kylawilson/Senior-Design-Sailboat-Nav-2025/HOUSING/Housing_main.png

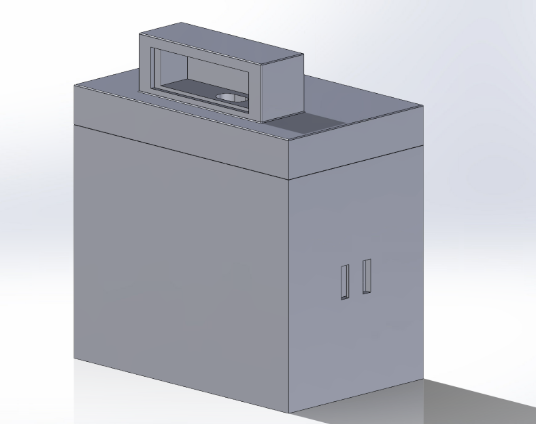
HOUSING/Housing_main.png
