kylawilson/Senior-Design-Sailboat-Nav-2025/HOUSING/Housing_sides.png

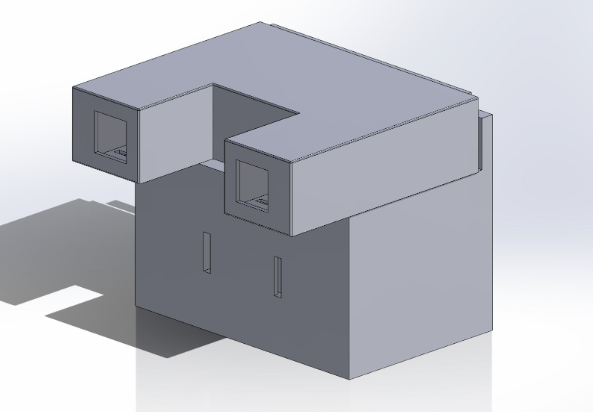
HOUSING/Housing_sides.png
