kylawilson/Senior-Design-Sailboat-Nav-2025/HOUSING/MountPoints.png

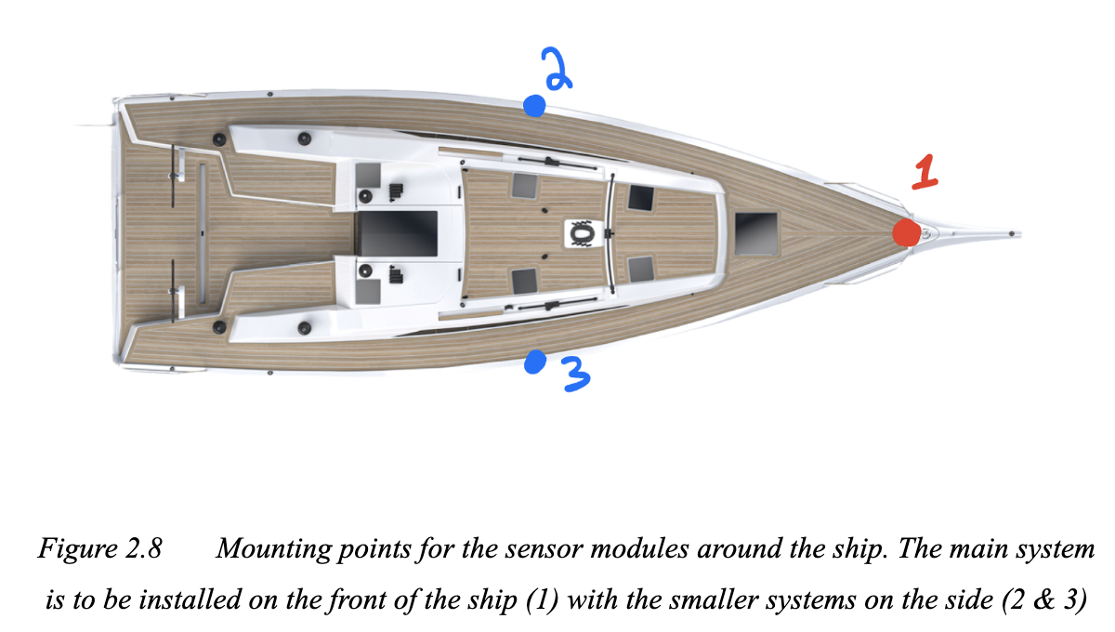
HOUSING/MountPoints.png
