kylawilson/Senior-Design-Sailboat-Nav-2025/OAK-D/outputframe.jpg

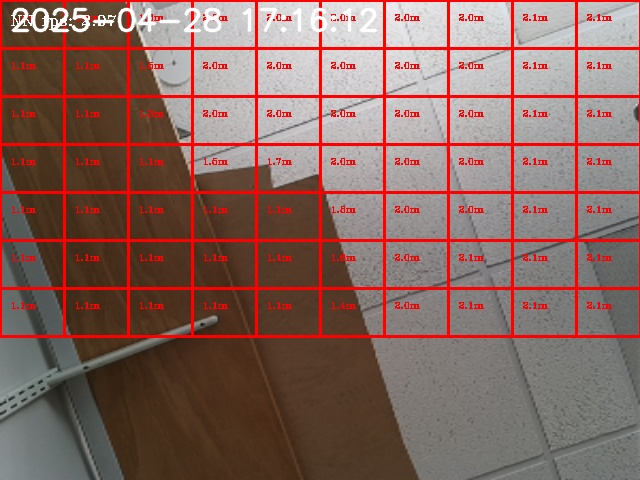
OAK-D/outputframe.jpg
