kylawilson/Senior-Design-Sailboat-Nav-2025/outputframe.jpg

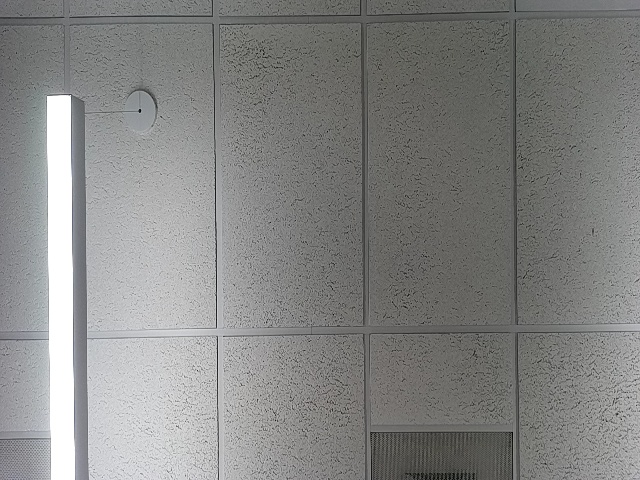
outputframe.jpg
