kylawilson/Senior-Design-Sailboat-Nav-2025/stereopi/normal.jpg

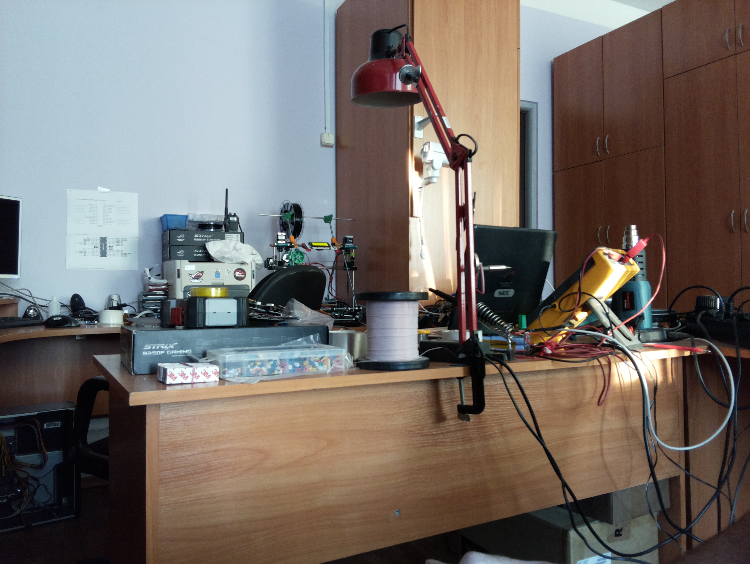
stereopi/normal.jpg
