kylawilson/Senior-Design-Sailboat-Nav-2025/stereopi/pairs/left_05.png

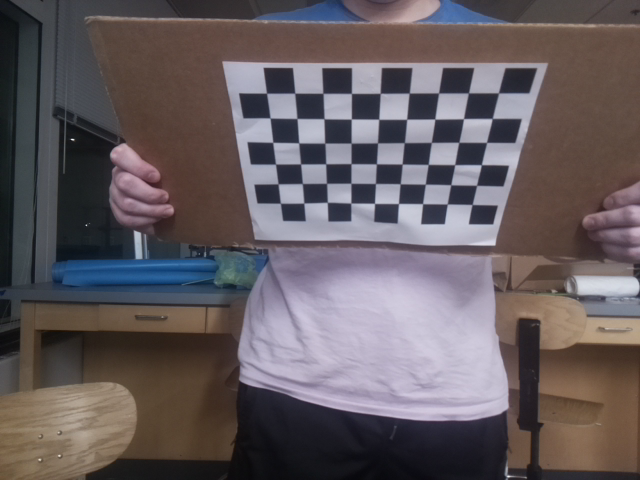
stereopi/pairs/left_05.png
