kylawilson/Senior-Design-Sailboat-Nav-2025/stereopi/pairs/left_09.png

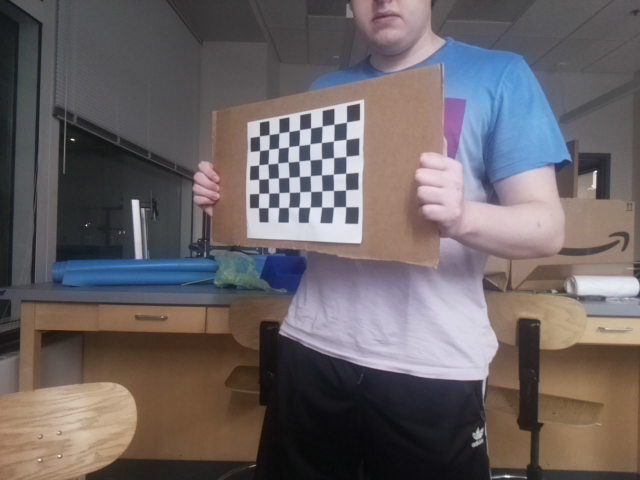
stereopi/pairs/left_09.png
