kylawilson/Senior-Design-Sailboat-Nav-2025/stereopi/pairs/left_13.png

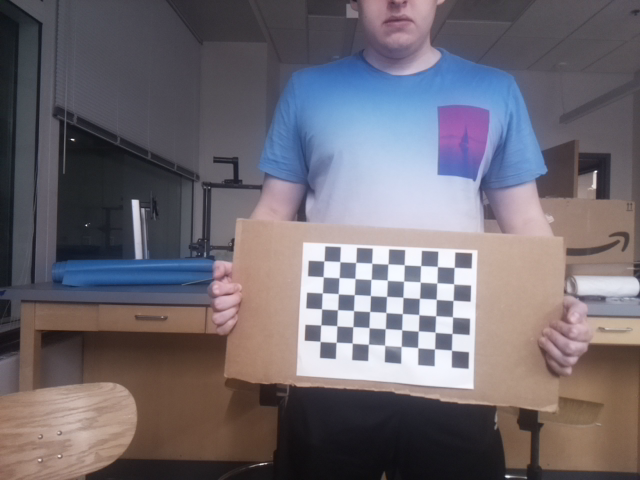
stereopi/pairs/left_13.png
