kylawilson/Senior-Design-Sailboat-Nav-2025/stereopi/pairs/left_14.png

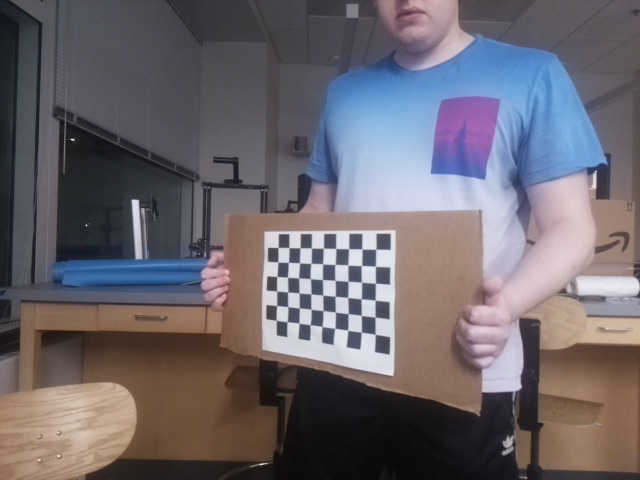
stereopi/pairs/left_14.png
