kylawilson/Senior-Design-Sailboat-Nav-2025/stereopi/pairs/left_15.png

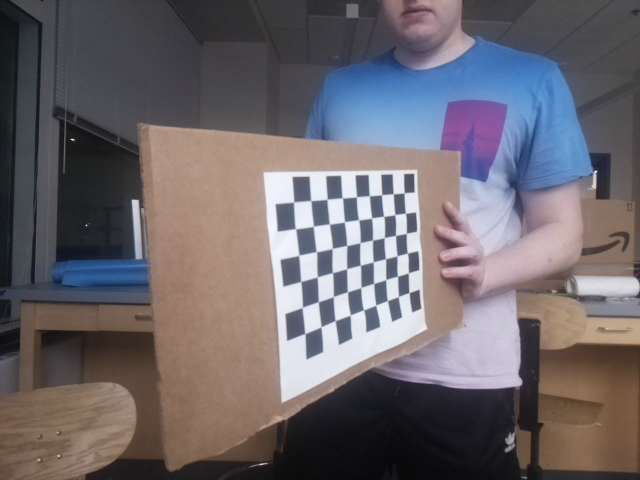
stereopi/pairs/left_15.png
