kylawilson/Senior-Design-Sailboat-Nav-2025/stereopi/pairs/left_23.png

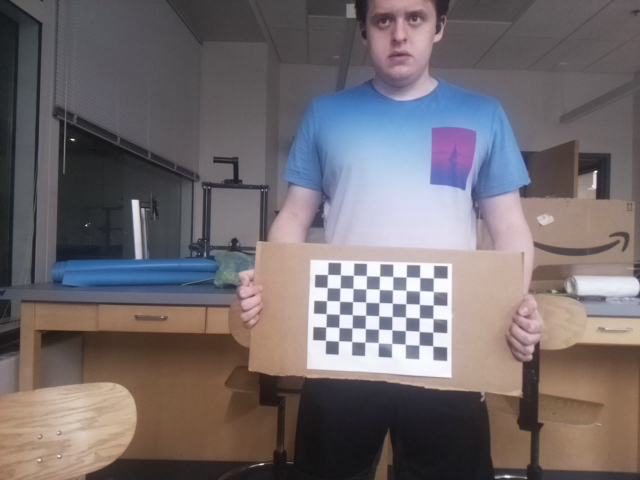
stereopi/pairs/left_23.png
