kylawilson/Senior-Design-Sailboat-Nav-2025/stereopi/pairs/right_08.png

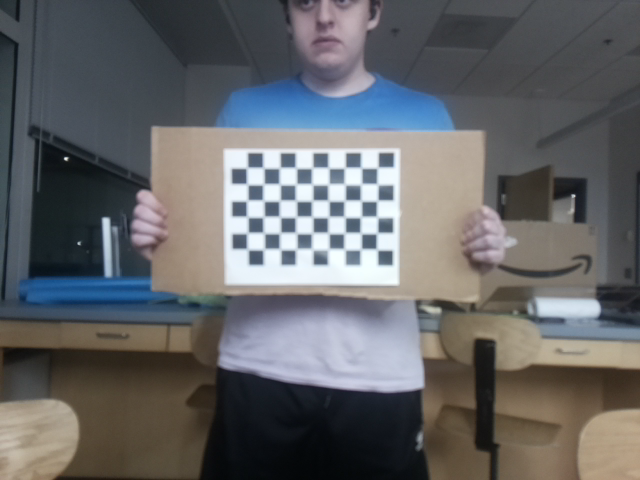
stereopi/pairs/right_08.png
