kylawilson/Senior-Design-Sailboat-Nav-2025/stereopi/pairs/right_13.png

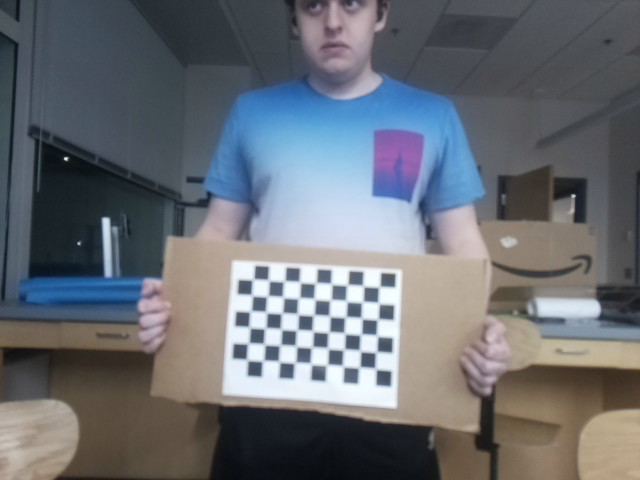
stereopi/pairs/right_13.png
