kylawilson/Senior-Design-Sailboat-Nav-2025/stereopi/pairs/right_22.png

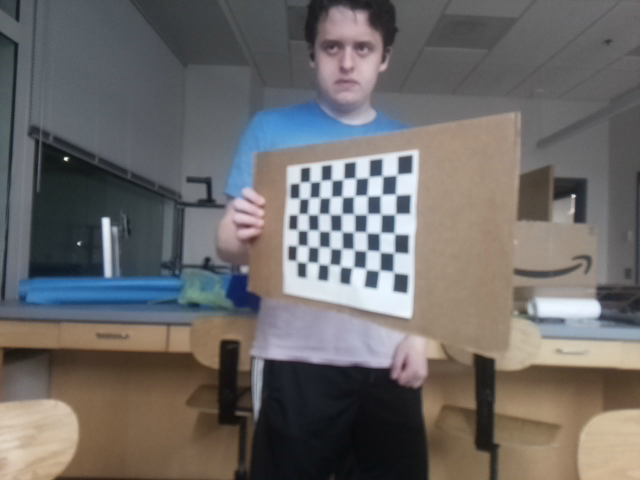
stereopi/pairs/right_22.png
