kylawilson/Senior-Design-Sailboat-Nav-2025/stereopi/pairs/right_31.png

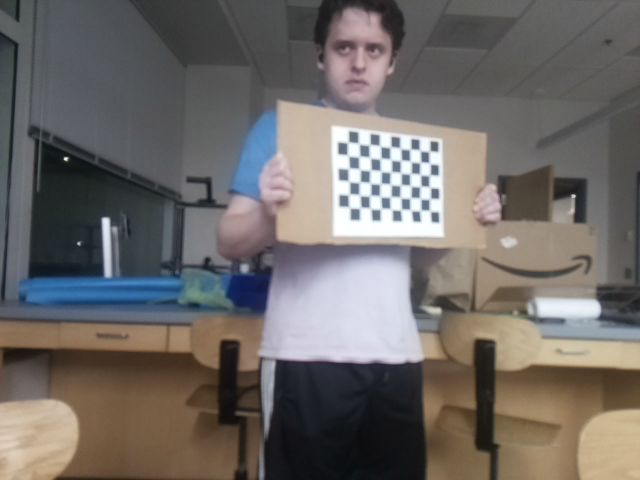
stereopi/pairs/right_31.png
