kylawilson/Senior-Design-Sailboat-Nav-2025/stereopi/pairs/right_32.png

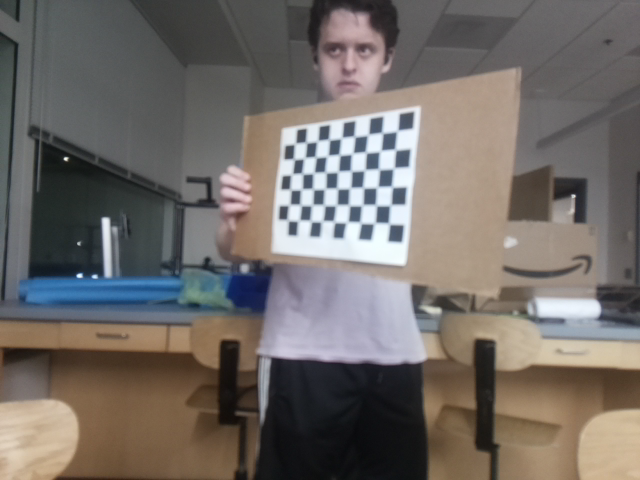
stereopi/pairs/right_32.png
