kylawilson/Senior-Design-Sailboat-Nav-2025/stereopi/pairs/right_40.png

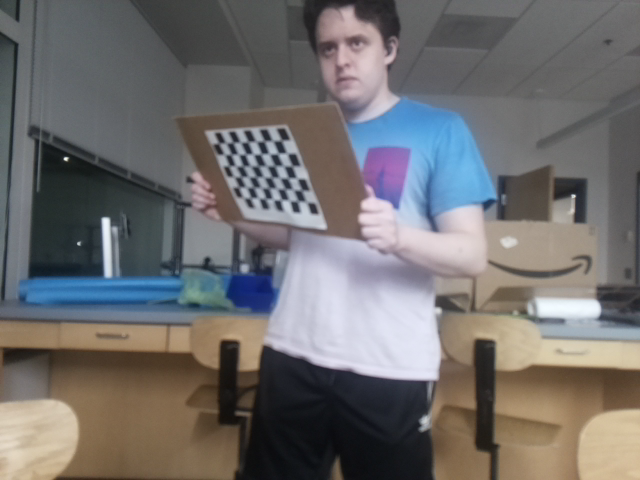
stereopi/pairs/right_40.png
