kylawilson/Senior-Design-Sailboat-Nav-2025/stereopi/pairs/right_41.png

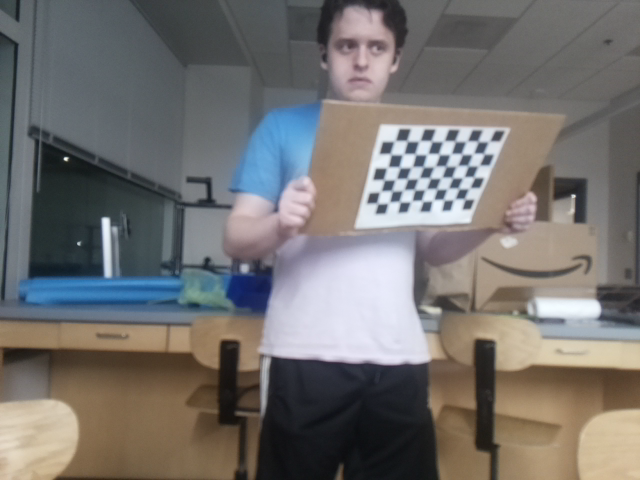
stereopi/pairs/right_41.png
