kylawilson/Senior-Design-Sailboat-Nav-2025/stereopi/pairs/right_43.png

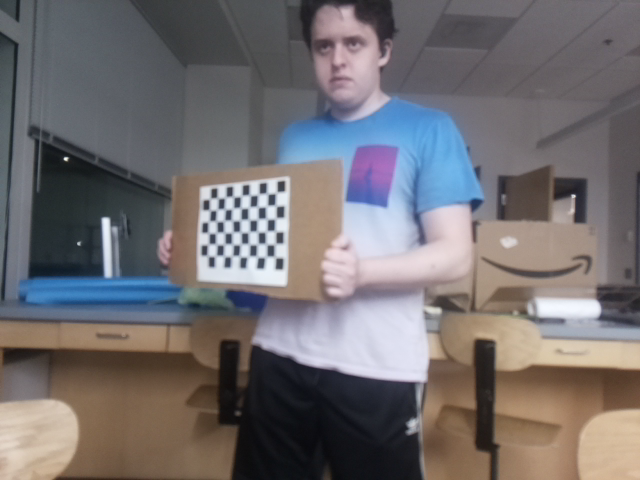
stereopi/pairs/right_43.png
