kylawilson/Senior-Design-Sailboat-Nav-2025/stereopi/pairs/right_49.png

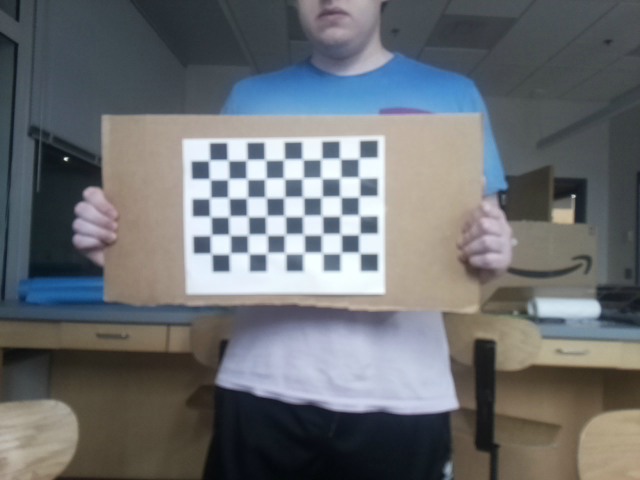
stereopi/pairs/right_49.png
