kylawilson/Senior-Design-Sailboat-Nav-2025/stereopi/rectifyed_left.jpg

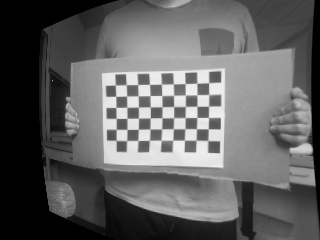
stereopi/rectifyed_left.jpg
