kylawilson/Senior-Design-Sailboat-Nav-2025/stereopi/rectifyed_right.jpg

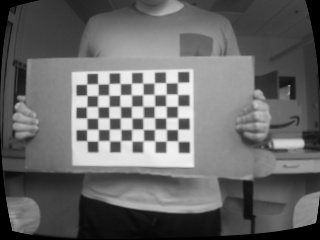
stereopi/rectifyed_right.jpg
