kylawilson/Senior-Design-Sailboat-Nav-2025/stereopi/scenes/photo.png

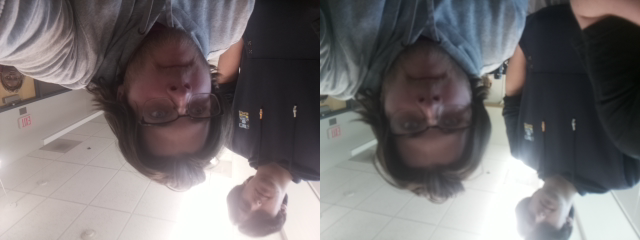
stereopi/scenes/photo.png
