kylawilson/Senior-Design-Sailboat-Nav-2025/stereopi/scenes/scene_640x240_22.png

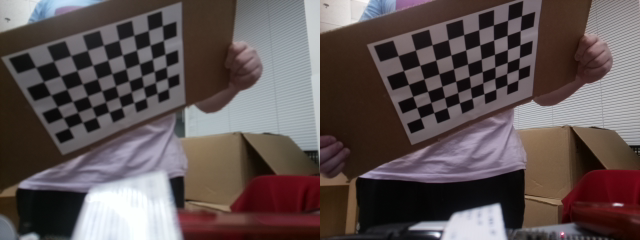
stereopi/scenes/scene_640x240_22.png
