kylawilson/Senior-Design-Sailboat-Nav-2025/stereopi/scenes/scene_1280x480_31.png

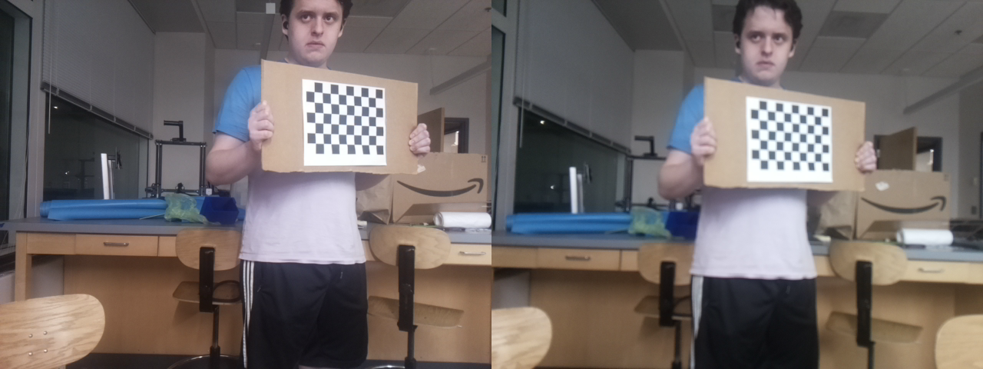
stereopi/scenes/scene_1280x480_31.png
