kylawilson/Senior-Design-Sailboat-Nav-2025/stereopi/undistorted_left.jpg

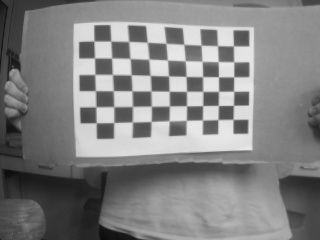
stereopi/undistorted_left.jpg
