kylawilson/Senior-Design-Sailboat-Nav-2025/stereopi/undistorted_right.jpg

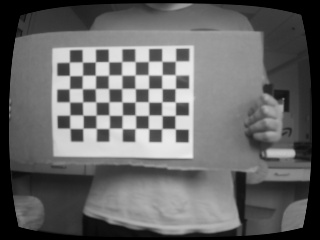
stereopi/undistorted_right.jpg
